hackerwarehouse/HW-DC25-Badge/src/HW-DC25-Badge/pkt1.h

#ifndef HW_PKT1_H
#define HW_PKT1_H

void Pkt_Monitor();   // remix of https://github.com/spacehuhn/PacketMonitor
void DeauthMonitor();  // remix of https://github.com/spacehuhn/DeauthDetector
void DeauthDetect();

#endif
