hackerwarehouse/HW-DC25-Badge/src/HW-DC25-Badge/core.h

#include <pgmspace.h>

#ifndef HW_CORE_H
#define HW_CORE_H

#define ESP8266
#define _CS  4    //for SSD_13XX.h
#define _DC  5    //for SSD_13XX.h
#define PIN            9
#define NUMPIXELS      14

#define MAXX 96
#define MAXY 64

#define REGION_ADDR 1           //1 byte - 1->US, 2->EU, 3->JP
#define PIXELBRIGHT_ADDR 2      //1 byte
#define MYDISPBRIGHT_ADDR 3     //1 byte
#define WS2812FXBRIGHT_ADDR 4   //1 byte
#define ARTWORK_ADDR 5          //1 byte
#define REGION_UNLOCK_ADDR 6    //1 byte

static const char UNLOCK_KONAMI[] PROGMEM  = {"UUDDLRLR"};
static const char UNLOCK_REGION[] PROGMEM  = {"RLRLLRDU"};
static const char UNLOCK_REGIONPERM[] PROGMEM  = {"UDDDUULR"};

#endif
